jreus/wearable_cape_v02/datasheets/Adafruit_GPS/gpsprint.png

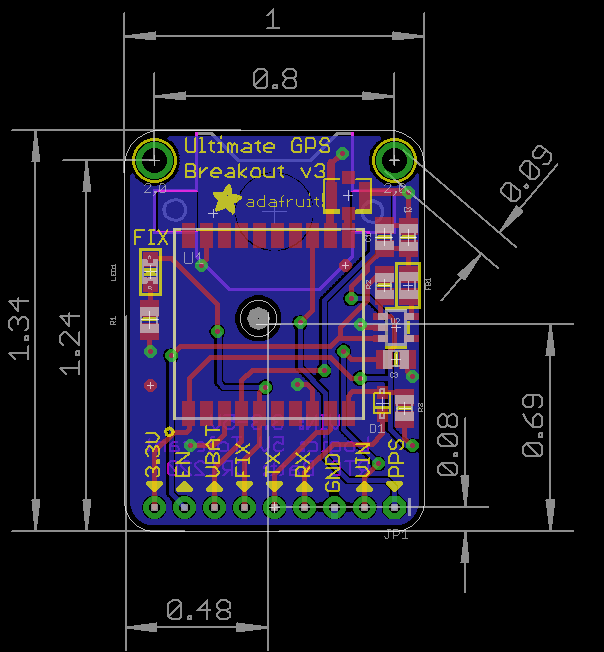
datasheets/Adafruit_GPS/gpsprint.png
