jreus/wearable_cape_v02/datasheets/MAX6100-Pinout.png

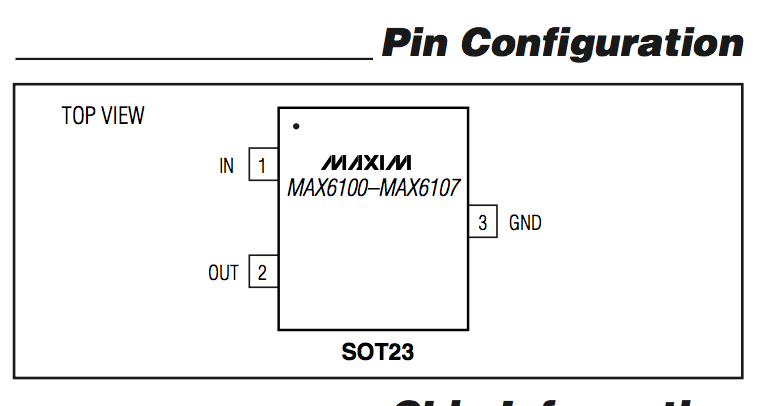
datasheets/MAX6100-Pinout.png
