jreus/wearable_cape_v02/datasheets/MAX6100-typical-circuit.png

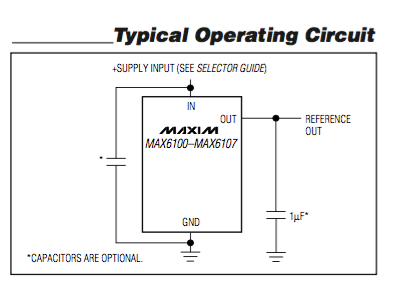
datasheets/MAX6100-typical-circuit.png
