jreus/wearable_cape_v02/images/REV2.1_wiring_mistake/CUTS-COLOR.png

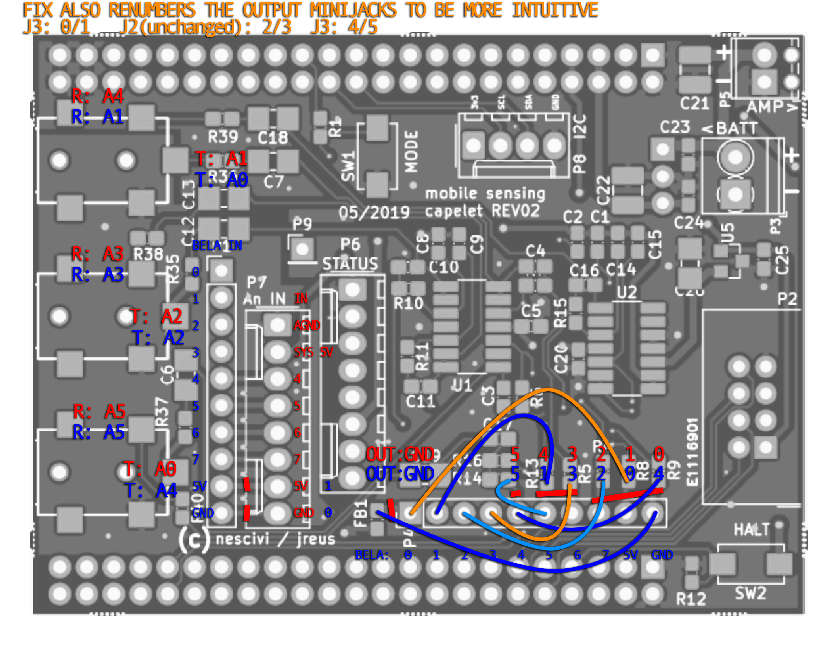
images/REV2.1_wiring_mistake/CUTS-COLOR.png
