jreus/wearable_cape_v02/images/REV2.1_wiring_mistake/REV2.1_pcb.png

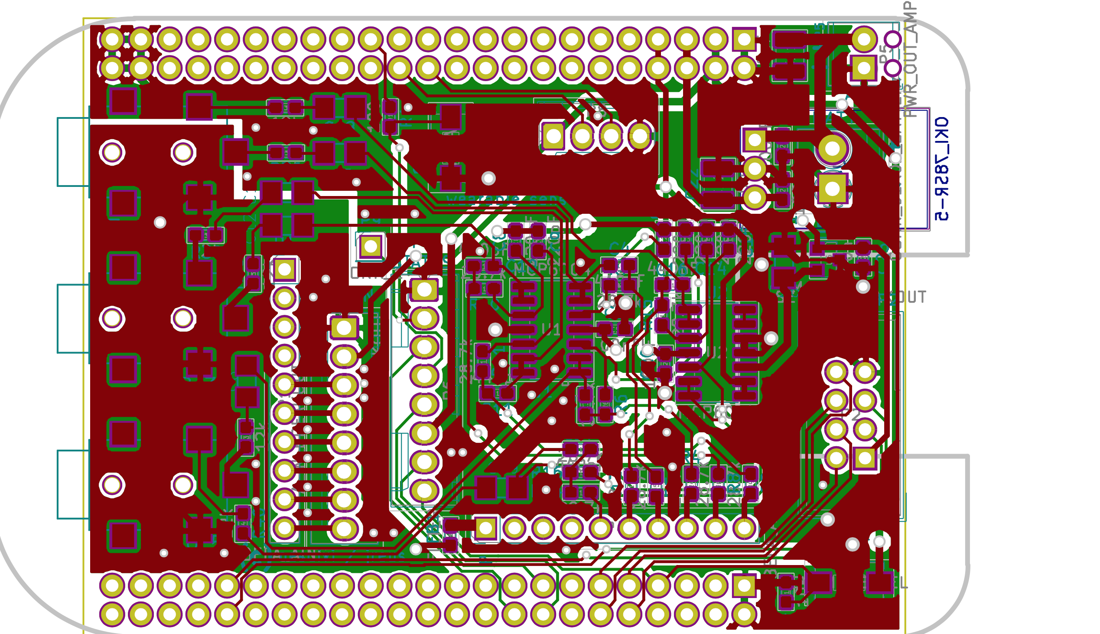
images/REV2.1_wiring_mistake/REV2.1_pcb.png
