jreus/wearable_cape_v02/images/REV2.1_wiring_mistake/Screen Shot 2019-05-23 at 22.55.19.png

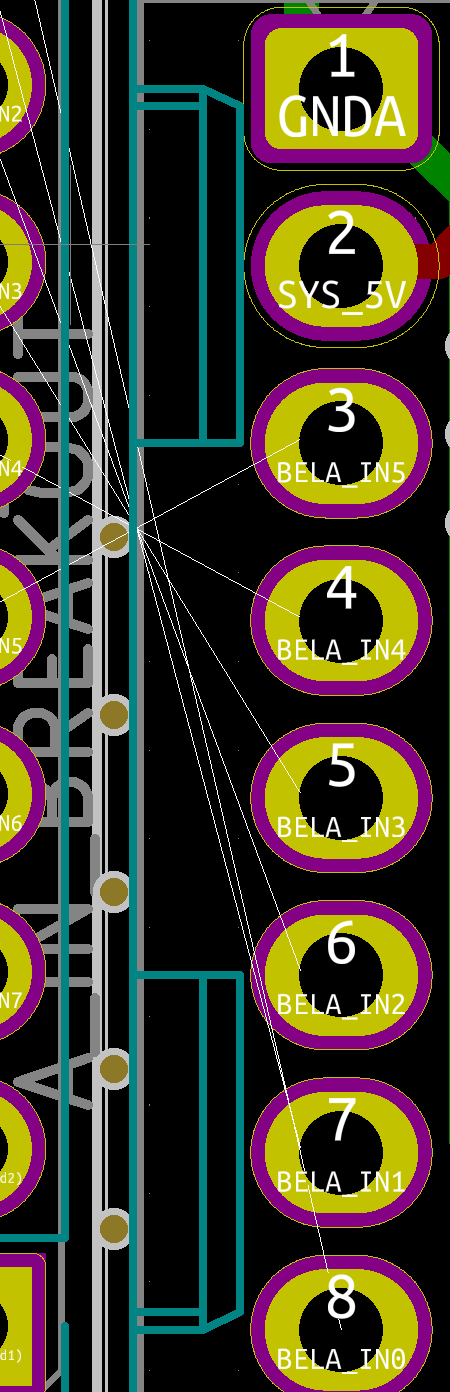
images/REV2.1_wiring_mistake/Screen Shot 2019-05-23 at 22.55.19.png
