jreus/wearable_cape_v02/images/REV2.1_wiring_mistake/Screen Shot 2019-05-27 at 19.33.47.png

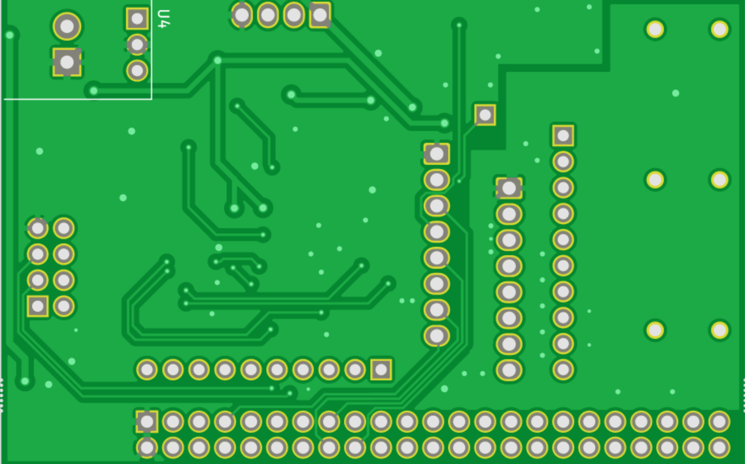
images/REV2.1_wiring_mistake/Screen Shot 2019-05-27 at 19.33.47.png
