jreus/wearable_cape_v02/simulations/Sallen-Key-Lowpass-with-3v-Attenuation.asc

BELA_AOUT1: voltage; ""; AC 2.45V 0; Rser=220
BELA_AOUT2: voltage; ""; AC 2.45V 0; Rser=220
BELA_AOUT3: voltage; ""; AC 2.45V 0; Rser=220
BELA_AOUT4: voltage; ""; AC 2.45V 0; Rser=220
BELA_AOUT5: voltage; ""; AC 2.45V 0; Rser=220
BELA_AOUT6: voltage; ""; AC 2.45V 0; Rser=220
BELA_AOUT: voltage; ""; AC 2.45V 0; Rser=220
C1: cap; 220pF
C2: cap; 440pF
C3: cap; 1µF
C4: cap; 220pF
C5: cap; 470pF
C6: cap; 1µF
C7: cap; 220pF
C8: cap; 470pF
C9: cap; 1µF
C10: cap; 220pF
C11: cap; 470pF
C12: cap; 1µF
C13: cap; 220pF
C14: cap; 470pF
C15: cap; 1µF
C16: cap; 220pF
C17: cap; 470pF
C18: cap; 1µF
C19: cap; 220pF
C20: cap; 470pF
C21: cap; 1µF
LOAD1: res; 20k
LOAD2: res; 20k
LOAD3: res; 20k
LOAD4: res; 20k
LOAD5: res; 20k
LOAD6: res; 20k
LOAD: res; 20k
R1: res; 28.7K
R2: res; 28.7K
R3: res; 28.7K
R4: res; 28.7K
R5: res; 150K
R6: res; 200K
R7: res; 28.7K
R8: res; 28.7K
R9: res; 28.7K
R10: res; 390
R11: res; 28.7K
R12: res; 2.2k
R13: res; 3.9k
R14: res; 28.7K
R15: res; 28.7K
R16: res; 220
R17: res; 390
R18: res; 28.7K
R19: res; 28.7K
R20: res; 2.2k
R21: res; 3.9k
R22: res; 28.7K
R23: res; 28.7K
R24: res; 2.2k
R25: res; 3.9k
R26: res; 12k
U1: EL5220C
U2: EL5220C
U3: EL5220C
U4: EL5220C
U5: EL5220C
U6: EL5220C
U7: EL5220C
U8: EL5220C
V1: voltage; 3.2V
V2: voltage; 1.8V
Named nets: V+, 0, 1.8V_REF, OUT_AUDIO_CAPE, OUT_NAIVE, OUT_ATT_PRE, OUT_ATT_POST1, OUT_ATT_POST2, OUT_ATT_BUF, OUT_ATT_POST1_SER
*.op
*.ac oct 100 1 400 *low frequencies
.ac oct 100 20 20000 *full frequencies
*.tran 0 10ms
*.step param R_LOAD list 1k 20k 100k
.inc "./models/el5220.txt"
To the left is a model of the low pass filter used on the Bela audio cape.
The input and output signal are ~4.7V peak-to-peak
The filter has a cutoff of around 17823.81Hz
The original op-amp used in the audio cape is a OPA4348 
(the ADD8704 is just for the Eagle footprint). 
The EL5420 is a similar op-amp which could also be used, 
the most important factor is Rail-to-Rail operation.
The analog outputs on the Bela have 220ohm series resistors for protection
1st try - make a filter that also attenuates the 0-4.7V signal to 3V peak-2-peak. 
I've swapped the 440pF cap for a more easily sourced 470pF cap.
The attenuation is ok, but compare the frequency response to the Audio capelet filter
The cutoff is somewhere around 2khz now! And it looks like I've added an extra zero into the curve.
2nd try - Andrew's suggestion to simply add a 390ohm resistor to the analog output.
Now the attenuation is ok and the frequency response is what we want (cutoff ~17khz)
The problem here is the power wasted via that small resistor to ground, which could 
draw up to 8mA of current from the DAC per channel
3rd try - Andrew's suggestion to attenuate after the filter.
The frequency response is good. But now the attenuation is highly dependent on the
input impedence of the load. The Adafruit amp (from what I can tell) has input impedance of 20k.
This creates an additional 6% attenuation of the output signal
4th try - Using lower value resistors on the output attenuator
the attenuation is now more exactly, and less dependent on load impedance. 
But now we're back to the problem of worst case up to 8mA being drawn by 
each op-amp per channel. The MCP6004 op-amps that we ended up using
can deliver up to 20mA, so shouldn't be a problem.
5th try - This design attenuates post filter and uses the larger value
resistors to keep power consumption low. Dependence on the load impedance
is eliminated using a buffer. 
This version has low power consumption, good filter behavior, at the expense
of another op-amp.
6th try - Finally, Andrew suggests using the load impedance of the
Adafruit board to our advantage.
He suggests putting a series resistor in line.
